MDOUBRE/TORPEDO/Photos/chassis_v1_2.JPG

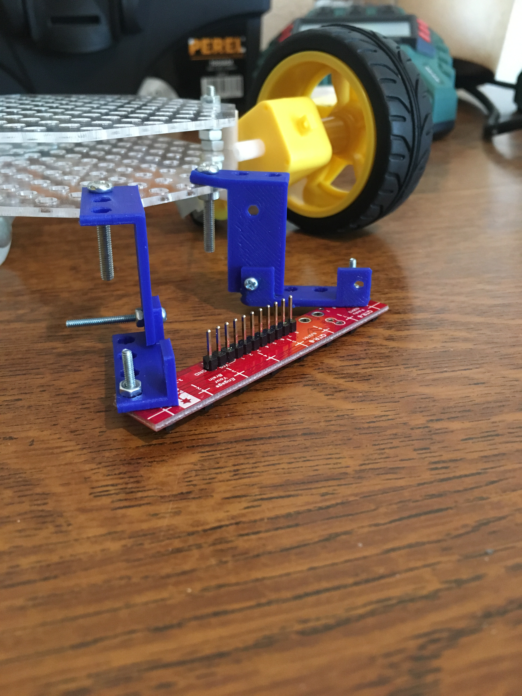
Photos/chassis_v1_2.JPG
