MDOUBRE/TORPEDO/Photos/chassis_v2_2.JPG

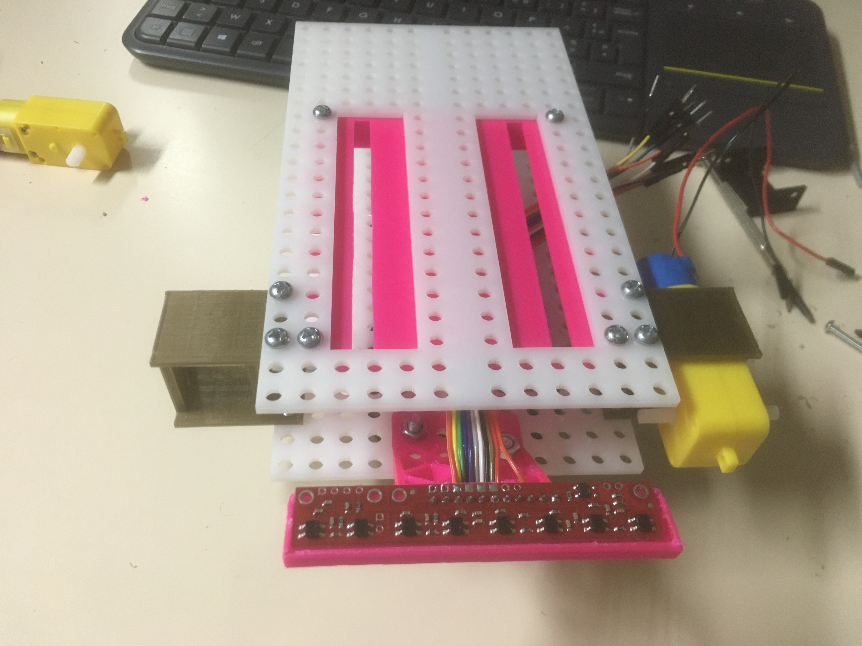
Photos/chassis_v2_2.JPG
