MDOUBRE/TORPEDO/Photos/chassis_v2_3.JPG

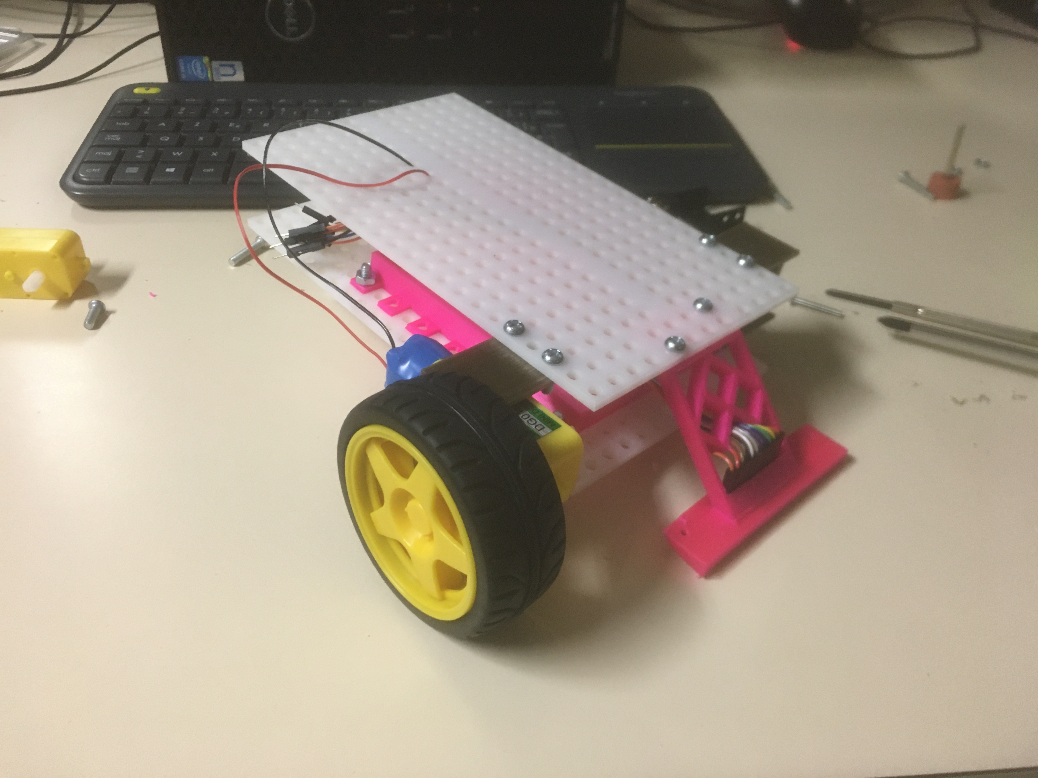
Photos/chassis_v2_3.JPG
