MDOUBRE/TORPEDO/Photos/chassis_v2_4.JPG

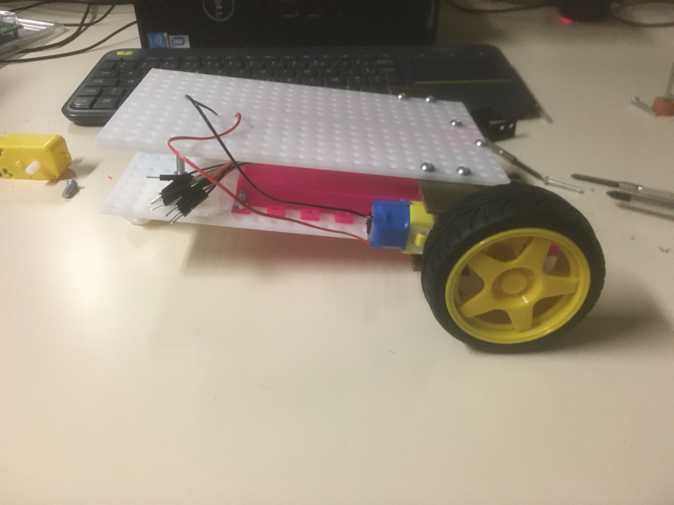
Photos/chassis_v2_4.JPG
