MDOUBRE/TORPEDO/Photos/chassis_v2_7.JPG

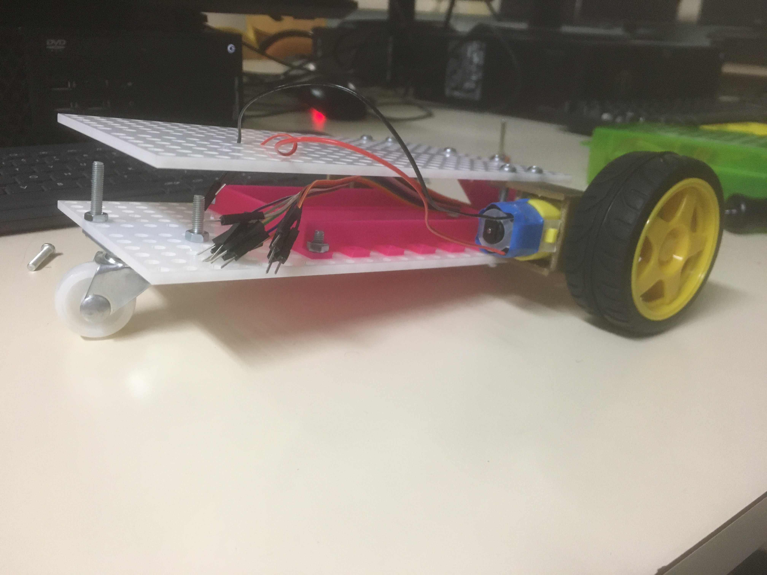
Photos/chassis_v2_7.JPG
