MDOUBRE/TORPEDO/Photos/controlleur_moteur_2.JPG

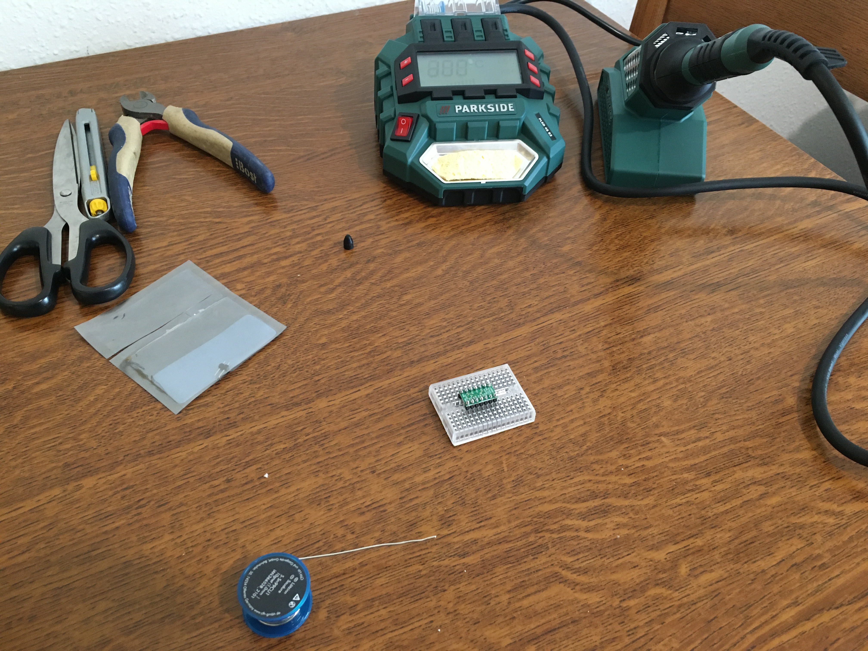
Photos/controlleur_moteur_2.JPG
