MDOUBRE/TORPEDO/Photos/test_moteurs_1.JPG

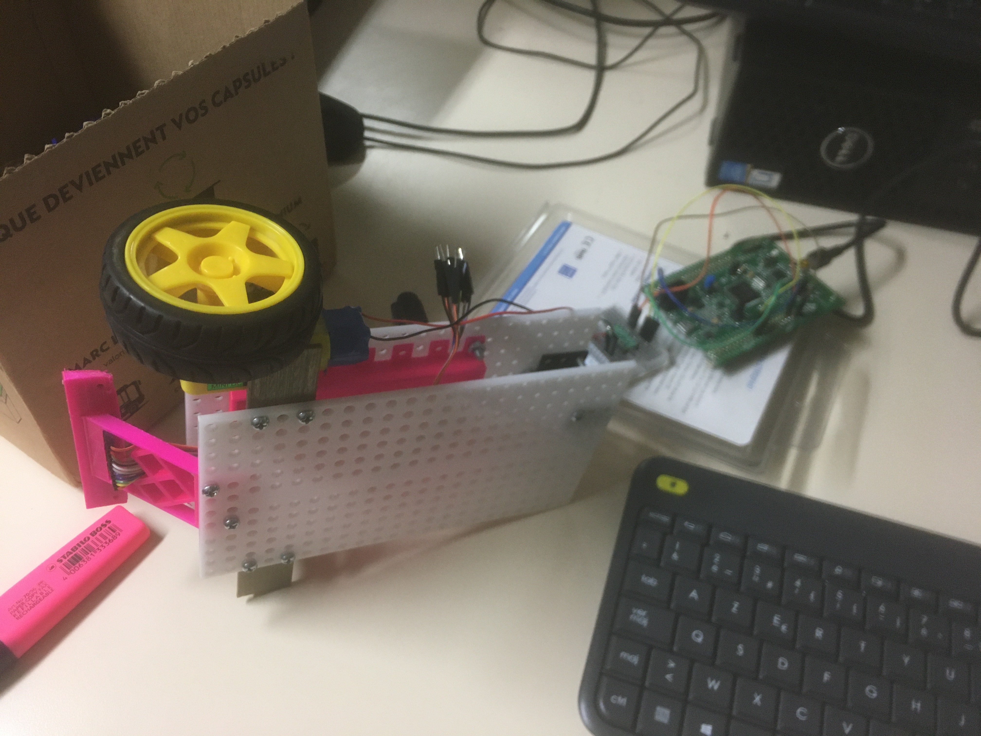
Photos/test_moteurs_1.JPG
