MDOUBRE/TORPEDO/Photos/test_moteurs_2.JPG

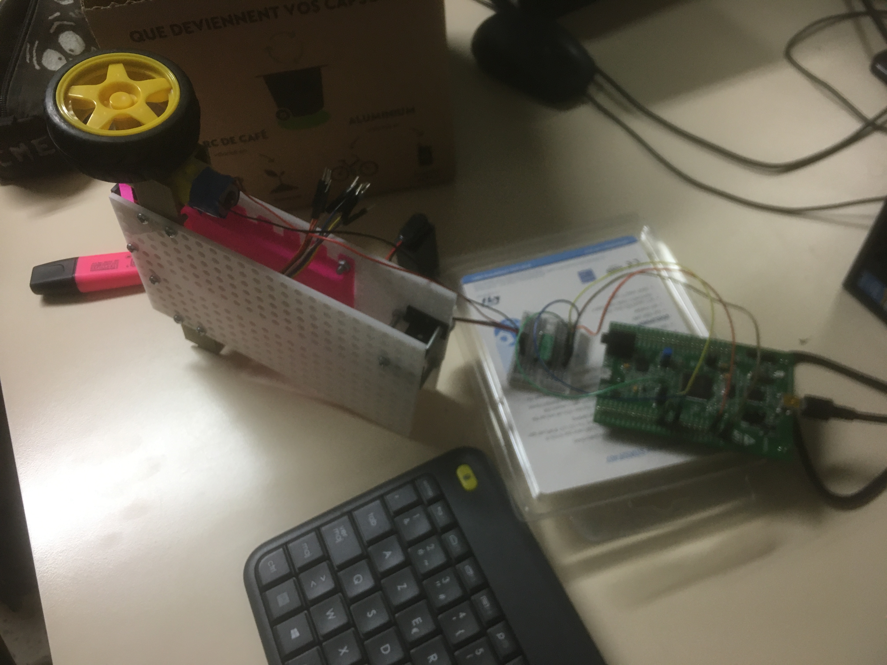
Photos/test_moteurs_2.JPG
