MDOUBRE/TORPEDO/Photos/test_moteurs_3.JPG

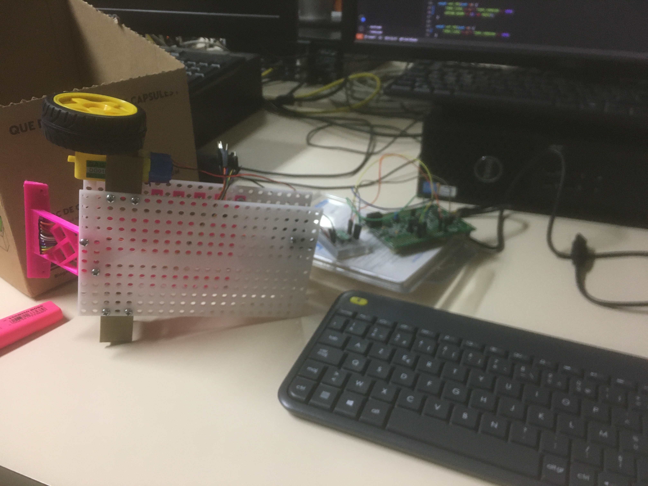
Photos/test_moteurs_3.JPG
