MDOUBRE/TORPEDO/code/include/stm32f4/adc.h

/**
 * Torpy - grid-follower wheeling and box delivering bot.
 *	Copyright (C) 2021  Université de Toulouse <casse@irit.fr>
 *
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
 *	This program is distributed in the hope that it will be useful,
 *	but WITHOUT ANY WARRANTY; without even the implied warranty of
 *	MERCHANTABILITY or FITNESS FOR A PARTICULAR PURPOSE.  See the
 *	GNU General Public License for more details.
 */
#ifndef STM32F4_DAC_H
#define STM32F4_DAC_H

#include "io.h"

#define ADC1_BASE	0x40012000
#define ADC2_BASE	0x40012100
#define ADC3_BASE	0x40012200
#define ADCC_BASE	0x40012300
#define ADC1_REG(o)	_IOREG(ADC1_BASE, o)
#define ADC2_REG(o)	_IOREG(ADC2_BASE, o)
#define ADC3_REG(o)	_IOREG(ADC3_BASE, o)
#define ADCC_REG(o)	_IOREG(ADCC_BASE, o)

#define ADC1_SR		ADC1_REG(0x00)
#define ADC2_SR		ADC2_REG(0x00)
#define ADC3_SR		ADC3_REG(0x00)
#define ADC_JEOC	(1 << 2)
#define ADC_EOC		(1 << 1)

#define ADC1_CR1	ADC1_REG(0x04)
#define ADC2_CR1	ADC2_REG(0x04)
#define ADC3_CR1	ADC3_REG(0x04)
#define ADC_OVERIE	(1 << 26)
#define ADC_12b		0b00
#define ADC_10n		0b01
#define ADC_8b		0b10
#define ADC_6b		0b11
#define ADC_JDISCEN	(1 << 12)
#define ADC_DISCEN	(1 << 11)
#define ADC_SCAN	(1 << 8)
#define ADC_EOCIE	(1 << 5)

#define ADC1_CR2	ADC1_REG(0x08)
#define ADC2_CR2	ADC2_REG(0x08)
#define ADC3_CR2	ADC3_REG(0x08)
#define ADC_SWSTART	(1 << 30)
#define ADC_JWSTART (1 << 22)
#define ADC_EOCS	(1 << 10)
#define ADC_CONT	(1 << 1)
#define ADC_ADON	(1 << 0)

#define ADC1_SMPR1	ADC1_REG(0x0C)
#define ADC2_SMPR1	ADC2_REG(0x0C)
#define ADC3_SMPR1	ADC3_REG(0x0C)

#define ADC1_SMPR2	ADC1_REG(0x10)
#define ADC2_SMPR2	ADC2_REG(0x10)
#define ADC3_SMPR2	ADC3_REG(0x10)

#define ADC1_JOFR(n)	ADC1_REG(0x14 + 4*(n))
#define ADC2_JOFR(n)	ADC2_REG(0x14 + 4*(n))
#define ADC2_JOFR(n)	ADC2_REG(0x14 + 4*(n))

#define ADC1_HTR	ADC1_REG(0x24)
#define ADC2_HTR	ADC2_REG(0x24)
#define ADC3_HTR	ADC3_REG(0x24)

#define ADC1_LTR	ADC1_REG(0x28)
#define ADC2_LTR	ADC2_REG(0x28)
#define ADC3_LTR	ADC3_REG(0x28)

#define ADC1_SQR1	ADC1_REG(0x2C)
#define ADC2_SQR1	ADC2_REG(0x2C)
#define ADC3_SQR1	ADC3_REG(0x2C)

#define ADC1_SQR2	ADC1_REG(0x30)
#define ADC2_SQR2	ADC2_REG(0x30)
#define ADC3_SQR2	ADC3_REG(0x30)

#define ADC1_SQR3	ADC1_REG(0x34)
#define ADC2_SQR3	ADC2_REG(0x34)
#define ADC3_SQR3	ADC3_REG(0x34)

#define ADC1_JSQR	ADC1_REG(0x38)
#define ADC2_JSQR	ADC2_REG(0x38)
#define ADC3_JSQR	ADC3_REG(0x38)

#define ADC1_JDR(n)	ADC1_REG(0x3C + 4*(n))
#define ADC2_JDR(n)	ADC2_REG(0x3C + 4*(n))
#define ADC2_JDR(n)	ADC2_REG(0x3C + 4*(n))

#define ADC1_DR		ADC1_REG(0x4C)
#define ADC2_DR		ADC2_REG(0x4C)
#define ADC2_DR		ADC2_REG(0x4C)

#define ADC_CSR		ADCC_REG(0x00)
#define ADC_CCR		ADCC_REG(0x04)
#define	ADC_DIV2	(0b00 << 16)
#define ADC_DIV4	(0b01 << 16)
#define ADC_DIV6	(0b10 << 16)
#define ADC_DIV8	(0b11 << 16)
#define ADC_CDR		ADCC_REG(0x08)

#endif	// STM32F4_GPIO_H
