MDOUBRE/TORPEDO/code/src/startup.c

/**
 *	Torpy - grid-follower wheeling and box delivering bot.
 *	Copyright (C) 2021  Université de Toulouse <casse@irit.fr>
 *
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
 *	This program is distributed in the hope that it will be useful,
 *	but WITHOUT ANY WARRANTY; without even the implied warranty of
 *	MERCHANTABILITY or FITNESS FOR A PARTICULAR PURPOSE.  See the
 *	GNU General Public License for more details.
 */

#include <stm32f4/dbg.h>
#include <stm32f4/rcc.h>
#include <stm32f4/syscfg.h>
#include <tinyprintf.h>

void handler_reset();
void handler_default();
void main();
void tiny_putc(void *, char c);


/*** linker script pointers ***/
extern uint32_t _data_flash;
extern uint32_t _data_begin;
extern uint32_t _data_end;
extern uint32_t _bss_begin;
extern uint32_t _bss_end;
extern uint32_t _stack_end;

/*** vector table ***/
__attribute__ ((section(".vector_table")))
void (* const table_interrupt_vector[256])() = {
	(void *)&_stack_end,// 0 - Stack
	handler_reset,		// 1 - Reset
	handler_default, 	// 2 - NMI (non maskable interrupt)
	handler_default, 	// 3 - Hard fault
	handler_default, 	// 4 - Memmanage fault (MPU violation or access to illegal location)
	handler_default, 	// 5 - Bus fault (bus error)
	handler_default, 	// 6 - Usage fault (program error eg acces coprocessor)
	0, 					// 7 - Reserved
	0, 					// 8 - Reserved
	0, 					// 9 - Reserved
	0, 					// 10 - Reserved
	handler_default,	// 11 - SVC (Supervisor call)
	handler_default,	// 12 - Debug monitor (BP, WP, external debug requests)
	0, 					// 13 - Reserved
	handler_default, 	// 14 - PendSV (pendable service call)
	handler_default, 	// 15 - SysTick (System tick timer)
	handler_default, 	// 0 -- ExtInt0 (External interrupt 0)
	handler_default,	// ...
	handler_default,
	handler_default,
	handler_default,
	handler_default,
	handler_default,
	handler_default,
	handler_default,
	handler_default,
	handler_default,
	handler_default,
	handler_default,
	handler_default,
	handler_default,
	handler_default, 
	handler_default, 
	handler_default, 
	handler_default, 
	handler_default, 
	handler_default,	// 20
	handler_default, 
	handler_default, 
	handler_default, 
	handler_default, 
	handler_default, 
	handler_default, 
	handler_default, 
	handler_default, 
	handler_default, 
	handler_default,	// 30
	handler_default, 
	handler_default, 
	handler_default, 
	handler_default, 
	handler_default, 
	handler_default, 
	handler_default, 
	handler_default, 
	handler_default, 
	handler_default,	// 40
	handler_default, 
	handler_default, 
	handler_default, 
	handler_default, 
	handler_default, 
	handler_default, 
	handler_default, 
	handler_default, 
	handler_default, 
	handler_default,	// 50
	handler_default, 
	handler_default, 
	handler_default, 
	handler_default, 
	handler_default, 
	handler_default, 
	handler_default, 
	handler_default, 
	handler_default,
	handler_default		// 60
};

#define FLASH_BASE	0x40023C00
#define FLASH_ACR	_IOREG(FLASH_BASE, 0x00)
#define FLASH_ACR_LATENCY_SET(x, l) _SET(x, 2, 0, l)
#define FLASH_ACR_DCEN	(1 << 10)
#define FLASH_ACR_ICEN	(1 << 9)


/*** reset handler ***/
void handler_reset() {
	uint32_t *p;
	uint32_t *q;
	uint32_t x;


	// copy data from FLASH to RAM
	p = &_data_flash;
	for(q = &_data_begin; q < &_data_end;)
			*q++ = *p++;

	// set to 0 BSS
	for(q = &_bss_begin; q < &_bss_end;)
		*q++ = 0;

	// configure clock
	// HSI clock = 16 MHz
	// HSE_VALUE <- 8 000 000 (8MHz - crystal frequency)
	// PLL_M <- 8 (/8 - 1MHz PLL)
	// MCK = (HS[EI]_CK / PLL_M) * PLL_N / PLL_P
	//	MCK		APB1	APB2	PLL_M	PLL_N	PLL_P	PLL_Q
	//	168		42		84		8		336		2		7

	// configure HSI clock
	RCC_CR |= RCC_CR_HSION;
	while((RCC_CR & RCC_CR_HSIRDY) == 0);
	RCC_CFGR_SW_SET(RCC_CFGR, RCC_HSI);

	// configure HSE clock
	RCC_CR |= RCC_CR_HSEON;
	while((RCC_CR & RCC_CR_HSERDY) == 0);

	// configure AHB and AHP[12]
	RCC_CFGGR_HPRE_SET(RCC_CFGR, RCC_HPRE_NODIV);
	RCC_CFGGR_PPRE1_SET(RCC_CFGR, RCC_PPRE_DIV4);
	RCC_CFGGR_PPRE2_SET(RCC_CFGR, RCC_PPRE_DIV2);

	// configure PLL
	RCC_CR &= ~RCC_CR_PLLON;
	x = 0;
	x |= RCC_PLLCFGR_SRC_HSE;
	RCC_PLLCFGR_M_SET(x, 8);
	RCC_PLLCFGR_N_SET(x, 336);
	RCC_PLLCFGR_P_SET(x, RCC_PLLP2);
	RCC_PLLCFGR_Q_SET(x, 7);
	RCC_PLLCFGR = x;
	RCC_CR |= RCC_CR_PLLON;
	while((RCC_CR & RCC_CR_PLLRDY) == 0);	

	// configure flash
	x = FLASH_ACR;
	x |= FLASH_ACR_DCEN;
	x |= FLASH_ACR_ICEN;
	FLASH_ACR_LATENCY_SET(x, 5);
	FLASH_ACR = x;
	
	// select PLL as SYSCLK
	RCC_CFGR_SW_SET(RCC_CFGR, RCC_PLL);
	while(RCC_CFGR_SWS_GET(RCC_CFGR) != RCC_PLL);
	RCC_CR &= ~RCC_CR_HSION;

	// rmap SRAM at 0
	SYSCFG_MEMRMP = 0b11;

	// console configuration
	DBG_DEMCR |= DBG_DEMCR_TRCENA;
	ITM_TRACE_EN |= ITM_TRACE_EN_PORT0;

	// run main
	init_printf(NULL, tiny_putc);
	main();
	while(1);
}

/*** default handler */
void handler_default() {
	while(1);
}

/**
 * Send character over ITM.
 * @param ch	Character to send.
 */
void ITM_putc(uint8_t ch) {

	// read FIFO status in bit [0]:
	while(!(ITM_STIMULUS_PORT0 & 1));

	//Write to ITM stimulus port0
	ITM_STIMULUS_PORT0 = ch;
}

/**
 * Interface with tinyprintf.
 */
void tiny_putc(void *_, char c) {
	ITM_putc(c);
}


/**
 * Send a string over ITEM.
 * @param s	String to send.
 */
void ITM_puts(const char *s) {
	while(*s)
		ITM_putc(*s++);
}
