MDOUBRE/TORPEDO/Photos/controlleur_moteur_1.JPG

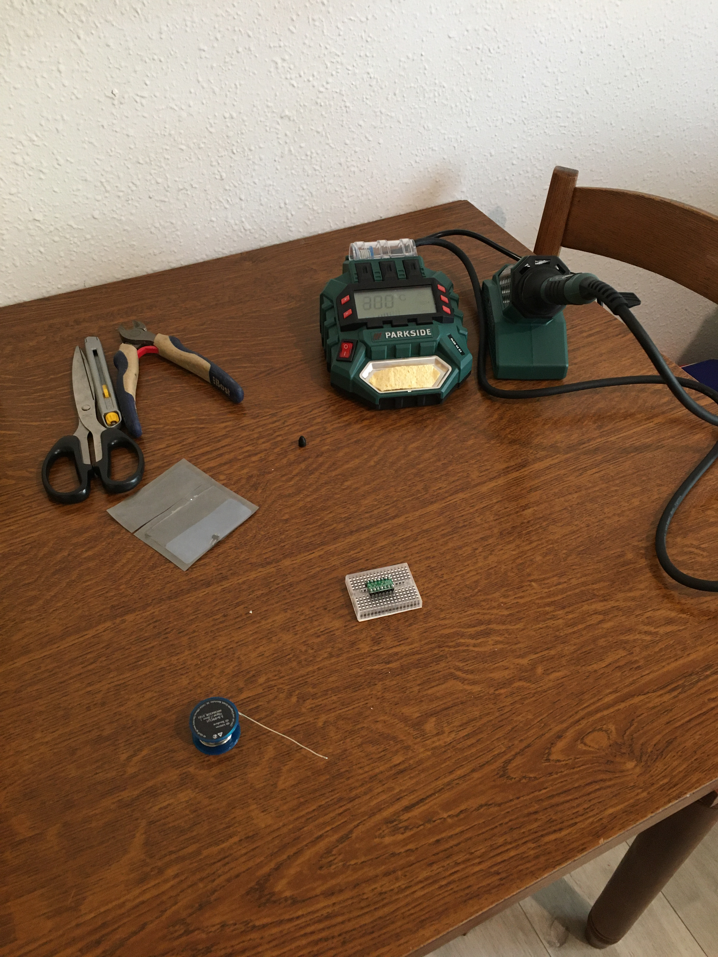
Photos/controlleur_moteur_1.JPG
